andrewrapp/arduino-remote-uploader/resources/breadboard-prototype.jpg

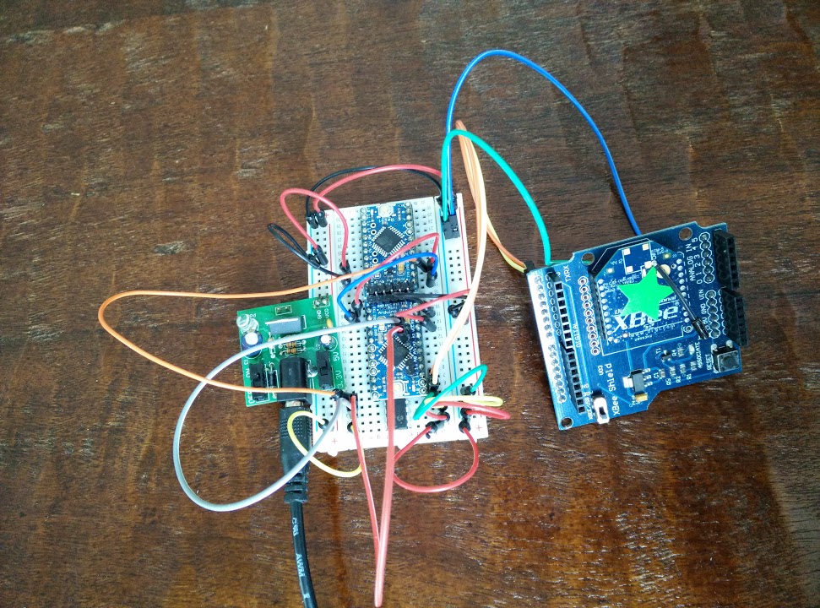
resources/breadboard-prototype.jpg
