andrewrapp/arduino-remote-uploader/resources/esp8266-arduino_bb.png

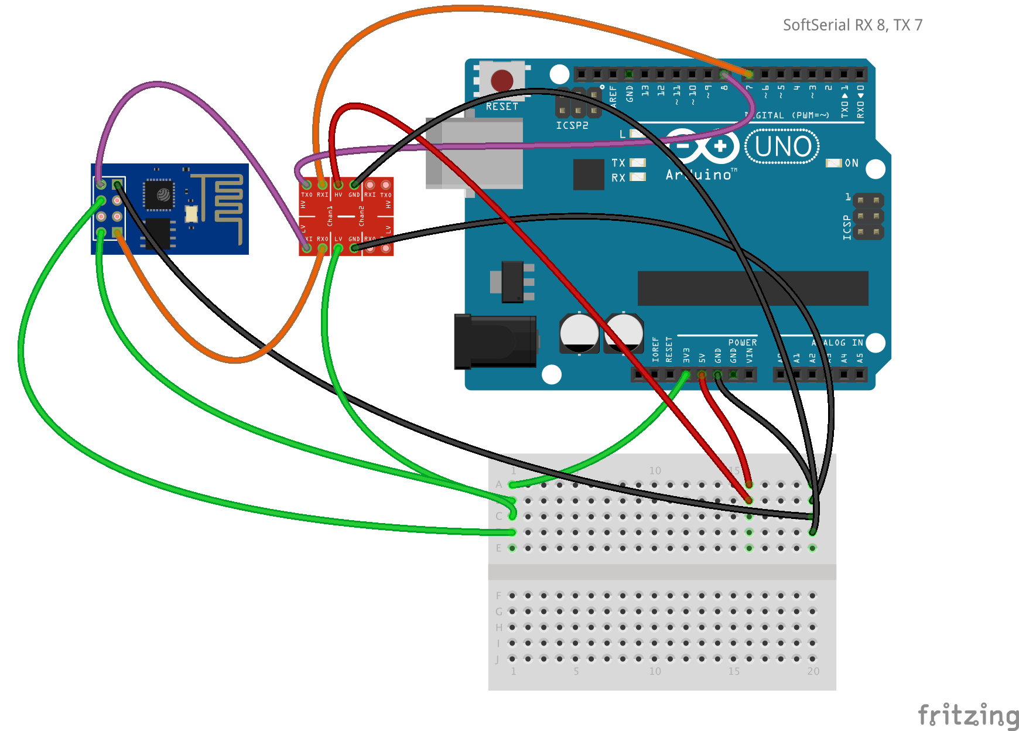
resources/esp8266-arduino_bb.png
