andrewrapp/arduino-remote-uploader/resources/ESP8266_V091.png

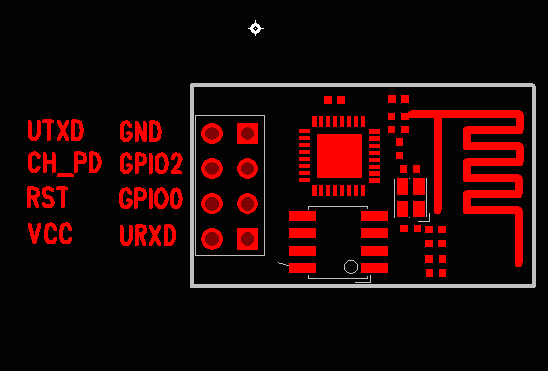
resources/ESP8266_V091.png
