andrewrapp/arduino-remote-uploader/resources/pocketprogrammer-pins.jpg

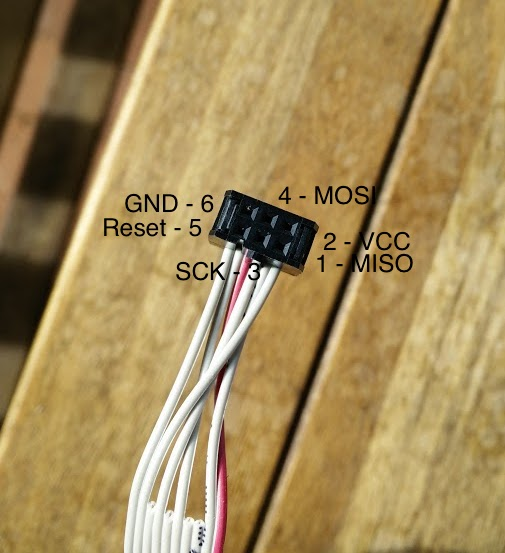
resources/pocketprogrammer-pins.jpg
